Tho85/ws2mqtt/Firmware-ESP/include/wifi_inc.h

#ifndef WIFI_H
#define WIFI_H 1

#include "Arduino.h"
#include <WiFi.h>
#include <PubSubClient.h>
#include "credentials.h"
#include "homeassistant.h"

boolean reconnectMQTT();
void mqttCallback(char* topic, byte* payload, unsigned int length);
void setupMQTT();
void loopMQTT();

void setupWifi();
#endif
